dansku/salo/vr/color_spectrum.framer/images/back.png

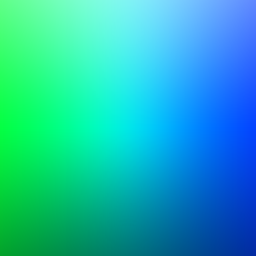
vr/color_spectrum.framer/images/back.png
